mertunsaldi/me462_hockey/Duvar Tasarımları/Bekirhan_Duvar/Bekirhan_Duvar_Tasarimi/Duvar_Tasarimi_Bekirin_Fikri_Top_View.jpg

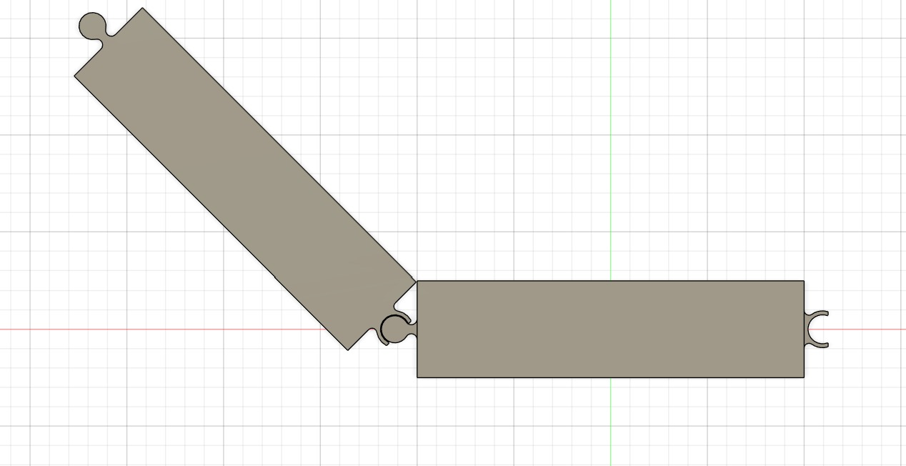
Duvar Tasarımları/Bekirhan_Duvar/Bekirhan_Duvar_Tasarimi/Duvar_Tasarimi_Bekirin_Fikri_Top_View.jpg
