mertunsaldi/me462_hockey/Duvar Tasarımları/Bekirhan_Duvar/Bekirhan_Duvar_Tasarimi/Duvar_Tasarimi_Mertin_Fikri_Iso_View.jpg

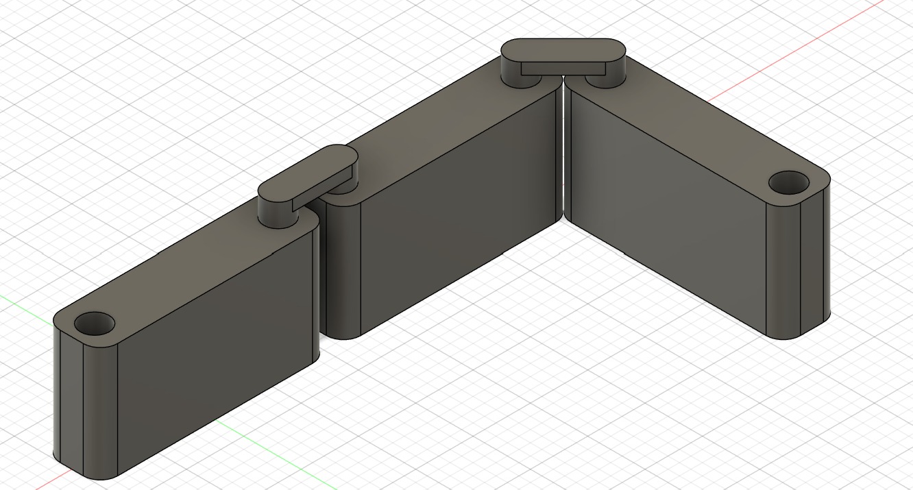
Duvar Tasarımları/Bekirhan_Duvar/Bekirhan_Duvar_Tasarimi/Duvar_Tasarimi_Mertin_Fikri_Iso_View.jpg
