mertunsaldi/me462_hockey/Duvar Tasarımları/Fatih/feet1_iso.png

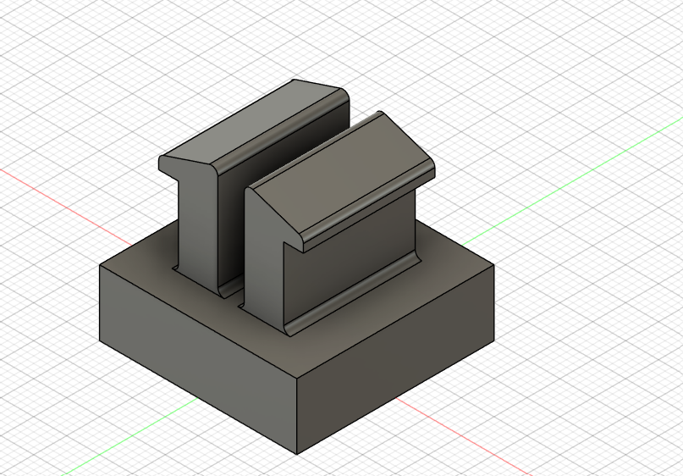
Duvar Tasarımları/Fatih/feet1_iso.png
