mertunsaldi/me462_hockey/Duvar Tasarımları/Fatih/assembly_0deg.png

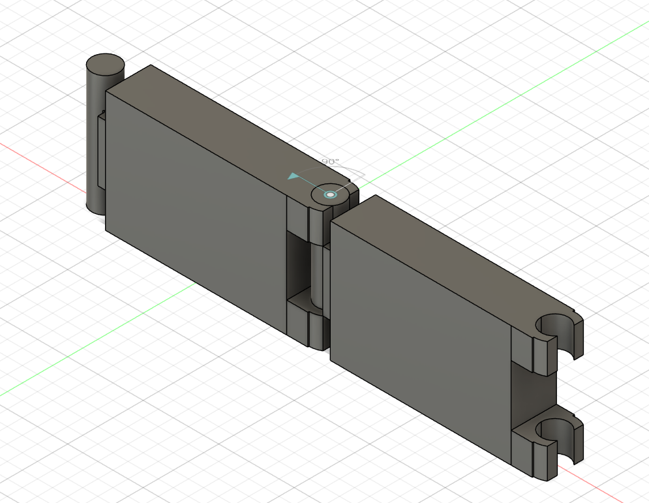
Duvar Tasarımları/Fatih/assembly_0deg.png
