mertunsaldi/me462_hockey/Duvar Tasarımları/Fatih/assembly_90deg_iso.png

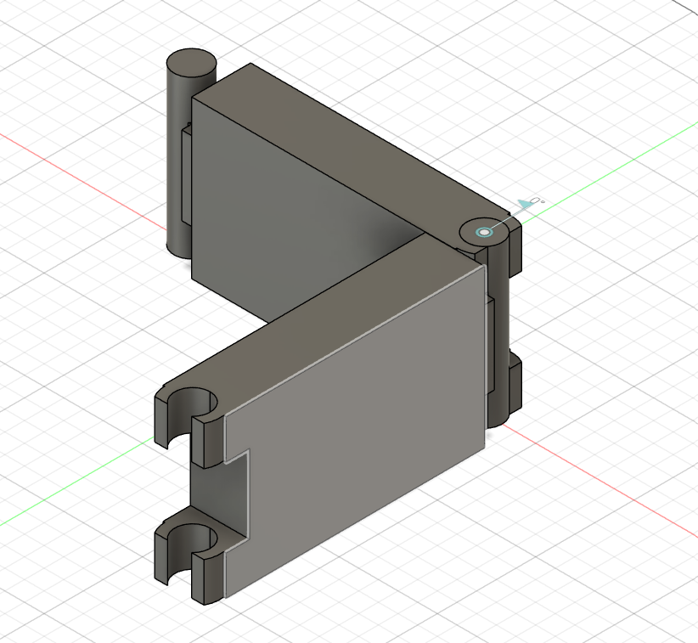
Duvar Tasarımları/Fatih/assembly_90deg_iso.png
