mertunsaldi/me462_hockey/Duvar Tasarımları/Fatih/assembly_90deg_top.png

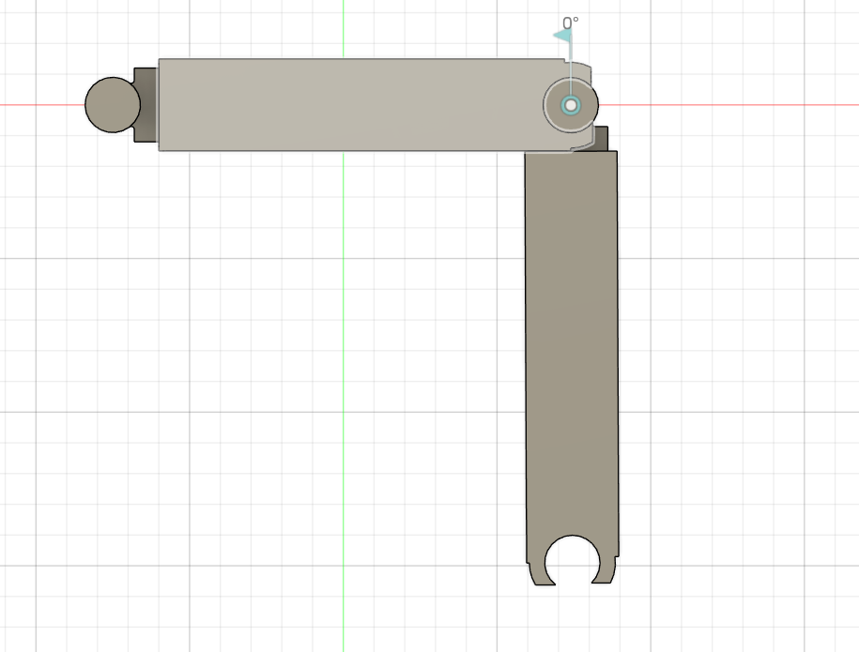
Duvar Tasarımları/Fatih/assembly_90deg_top.png
