mertunsaldi/me462_hockey/Duvar Tasarımları/Seckin/Assembly.png

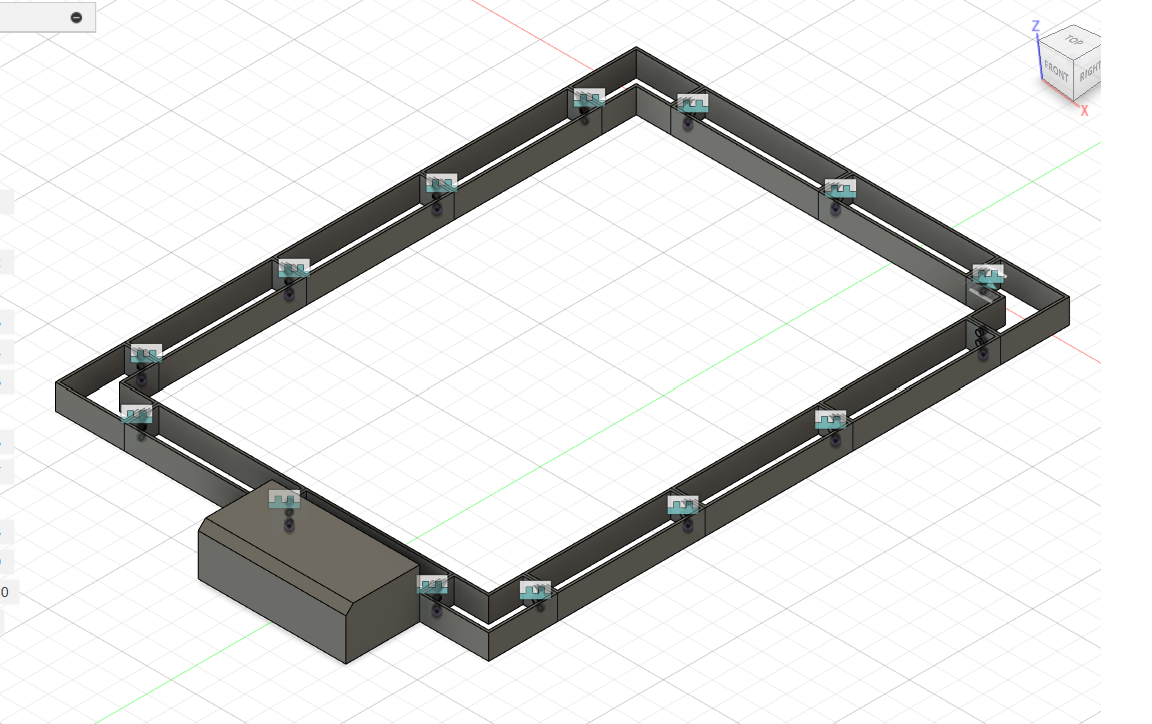
Duvar Tasarımları/Seckin/Assembly.png
