mertunsaldi/me462_hockey/ball_example/app.py

import cv2, math, threading, time
import numpy as np
from typing import Optional
from flask import Flask, render_template, Response, jsonify, request
import os

if __package__ in (None, ""):
    import os, sys
    sys.path.insert(0, os.path.abspath(os.path.join(os.path.dirname(__file__), "..")))
    __package__ = "ball_example"

from ball_example.game_api import GameAPI
from ball_example.scenario_loader import ScenarioLoadError
from ball_example.detectors import BallDetector, compute_color_mask, ArucoDetector
from ball_example.trackers import DETECTION_SCALE
from ball_example.models import ArucoWall, Arena, Obstacle, PhysicalTarget
from ball_example.gadgets import ArenaManager, PlotClock
from ball_example.high_level import calibrate_clocks, draw_arena

app = Flask(__name__, template_folder="templates", static_folder="static")

import logging

log = logging.getLogger("werkzeug")
log.setLevel(logging.ERROR)

# Core processing API
POLY_PATH = os.path.abspath(
    os.path.join(os.path.dirname(__file__), "..", "PlotClock", "calibration_poly.csv")
)
api = GameAPI(coeffs_path=POLY_PATH)
api.set_cam_source(4, width=1280, height=720, fourcc="MJPG")

if hasattr(app, "before_first_request"):
    @app.before_first_request
    def _ensure_camera_running():
        api.start()
else:
    @app.before_request
    def _ensure_camera_running():
        api.start()
        
# Manual tuning state
manual_mode = False
detected_clocks = []
detected_arena = None
_default_params = {
    "circ": BallDetector.CIRCULARITY_THRESHOLD,
    "area_ratio": BallDetector.AREA_RATIO_THRESHOLD,
    "solidity": BallDetector.SOLIDITY_THRESHOLD,
    "edge_density": BallDetector.EDGE_DENSITY_THRESHOLD,
    "blur": BallDetector.BLUR_KERNEL,
    "sigma": BallDetector.BLUR_SIGMA,
    "min_r": BallDetector.MIN_RADIUS,
    "max_r": BallDetector.MAX_RADIUS,
    "h_low": int(BallDetector.HSV_LOWER[0]),
    "s_low": int(BallDetector.HSV_LOWER[1]),
    "v_low": int(BallDetector.HSV_LOWER[2]),
    "h_up": int(BallDetector.HSV_UPPER[0]),
    "s_up": int(BallDetector.HSV_UPPER[1]),
    "v_up": int(BallDetector.HSV_UPPER[2]),
}
_manual_params = _default_params.copy()

def _apply_params(params):
    BallDetector.CIRCULARITY_THRESHOLD = float(params["circ"])
    BallDetector.AREA_RATIO_THRESHOLD  = float(params["area_ratio"])
    BallDetector.SOLIDITY_THRESHOLD    = float(params["solidity"])
    BallDetector.BLUR_KERNEL = int(params["blur"])
    BallDetector.BLUR_SIGMA  = float(params["sigma"])
    BallDetector.EDGE_DENSITY_THRESHOLD= float(params["edge_density"])
    BallDetector.MIN_RADIUS = int(params["min_r"])
    BallDetector.MAX_RADIUS = int(params["max_r"])
    BallDetector.HSV_LOWER = np.array([params["h_low"], params["s_low"], params["v_low"]], dtype=np.uint8)
    BallDetector.HSV_UPPER = np.array([params["h_up"], params["s_up"], params["v_up"]], dtype=np.uint8)

def _reset_defaults():
    global _manual_params
    _manual_params = _default_params.copy()
    _apply_params(_default_params)


# ------------------------------------------------------------------


@app.route("/start_scenario", methods=["POST"])
def start_scenario():
    """Activate the currently loaded scenario."""
    try:
        api.start_scenario()
        return jsonify({"status": "ok"})
    except Exception as e:
        return jsonify({"status": "error", "message": str(e)}), 400


@app.route("/stop_scenario", methods=["POST"])
def stop_scenario():
    """Deactivate the running scenario if any."""
    try:
        api.stop_scenario()
        return jsonify({"status": "ok"})
    except Exception as e:
        return jsonify({"status": "error", "message": str(e)}), 400


@app.route("/load_commands", methods=["POST"])
def load_commands():
    data = request.get_json(silent=True) or {}
    commands = data.get("commands")
    if not isinstance(commands, list):
        return jsonify({"status": "error", "message": "commands must be a list"}), 400
    try:
        api.load_commands(commands)
        return jsonify({"status": "ok"})
    except Exception as e:
        return jsonify({"status": "error", "message": str(e)}), 400


@app.route("/load_scenario", methods=["POST"])
def load_scenario_route():
    """Load a custom scenario from a Python file path or uploaded file."""
    if "file" in request.files:
        up = request.files["file"]
        path = "/tmp/" + up.filename
        up.save(path)
    else:
        data = request.get_json(silent=True) or {}
        path = data.get("path")
    if not path:
        return jsonify({"status": "error", "message": "no path provided"}), 400
    try:
        api.load_scenario(path)
        return jsonify({"status": "ok"})
    except ScenarioLoadError as e:
        return jsonify({"status": "error", "message": str(e)}), 400
    except RuntimeError as e:
        # allow missing plotclock during testing
        return jsonify({"status": "error", "message": str(e)})
    except Exception as e:
        return jsonify({"status": "error", "message": str(e)}), 500




def generate_frames():
    while True:
        annotated = api.get_annotated_frame()
        if annotated is None:
            time.sleep(0.01)
            continue

        with api.lock:
            dets = api.balls + api.arucos

        if detected_arena:
            draw_arena(annotated, detected_arena)
        for c in detected_clocks:
            c.draw_working_area(annotated)

        ok, buf = cv2.imencode(".jpg", annotated)
        if not ok:
            continue

        yield (
            b"--frame\r\n" b"Content-Type: image/jpeg\r\n\r\n" + buf.tobytes() + b"\r\n"
        )



@app.route("/")
def index():
    return render_template("index.html")


@app.route("/video_feed")
def video_feed():
    return Response(
        generate_frames(), mimetype="multipart/x-mixed-replace; boundary=frame"
    )


@app.route("/debug_data")
def debug_data():
    """Return extended diagnostic information."""
    return jsonify(api.debug_info())


@app.route("/connect_pico", methods=["POST"])
def connect_pico():
    global detected_clocks, detected_arena
    try:
        api.connect_pico()

        print("Waiting for detections...")
        detected_clocks = []
        detected_arena = None
        start = time.time()
        while time.time() - start < 5:
            time.sleep(0.1)
            with api.lock:
                detections = list(api.arucos)
                detected_clocks = list(api.plotclocks.values())
            if detected_arena is None:
                walls = [d for d in detections if isinstance(d, ArucoWall)]
                if walls:
                    detected_arena = Arena(walls)

        if detected_arena:
            for c in detected_clocks:
                if isinstance(c, ArenaManager):
                    c.set_arena(detected_arena)

        if detected_clocks:
            stable_start = time.time()
            last_count = len(detected_clocks)
            while time.time() - stable_start < 1.0:
                time.sleep(0.1)
                with api.lock:
                    detected_clocks = list(api.plotclocks.values())
                if len(detected_clocks) == last_count:
                    break
                last_count = len(detected_clocks)
                stable_start = time.time()

        # if both a manager (P0) and a hitter (P1) are detected, prepare the
        # built-in default scenario so it can be started via the UI
        manager = next(
            (c for c in detected_clocks if isinstance(c, ArenaManager) and c.device_id == 0),
            None,
        )
        hitter = next(
            (c for c in detected_clocks if isinstance(c, PlotClock) and c.device_id == 1),
            None,
        )
        if manager and hitter:
            api.default_scenario = "MoveBallHitRandom"
            api.load_default_scenario()
        else:
            api.default_scenario = None

        return jsonify({"status": "ok"})
    except Exception as e:
        return jsonify({"status": "error", "message": str(e)}), 500


@app.route("/calibrate_all", methods=["POST"])
def calibrate_all():
    """Calibrate all detected PlotClocks."""
    global detected_clocks
    with api.lock:
        clocks = list(api.plotclocks.values())
    if not clocks:
        return jsonify({"status": "error", "message": "no plotclocks"}), 400

    detected_clocks = clocks

    def _get_dets():
        with api.lock:
            return api.balls + api.arucos

    calibrate_clocks(clocks, _get_dets)
    return jsonify({"status": "ok"})


@app.route("/toggle_mode", methods=["POST"])
def toggle_mode():
    """Start or stop a scenario for a specific PlotClock."""
    data = request.get_json(silent=True) or {}
    device_id = int(data.get("device_id", -1))
    mode = data.get("mode")
    clock = api.plotclocks.get(device_id)
    if clock is None or mode not in {"attack", "defend", "hit_standing"}:
        return jsonify({"status": "error", "message": "invalid"}), 400

    x_mm = y_mm = None
    if mode in {"attack", "hit_standing"}:
        try:
            x_mm = float(data.get("x"))
            y_mm = float(data.get("y"))
        except (TypeError, ValueError):
            return jsonify({"status": "error", "message": "invalid"}), 400

    if api.clock_modes.get(device_id) == mode:
        api.stop_clock_mode(device_id)
        return jsonify({"status": "stopped"})

    # replace any running scenario on this clock
    if device_id in api.clock_scenarios:
        api.stop_clock_mode(device_id)

    api.start_clock_mode(clock, mode, target_mm=(x_mm, y_mm))
    api.set_preview_target(device_id, (x_mm, y_mm)) if x_mm is not None else None
    return jsonify({"status": "started"})


@app.route("/move_object", methods=["POST"])
def move_object_route():
    data = request.get_json(silent=True) or {}
    device_id = int(data.get("device_id", -1))
    obj_spec = data.get("object")
    try:
        x_mm = float(data.get("x"))
        y_mm = float(data.get("y"))
    except (TypeError, ValueError):
        return jsonify({"status": "error", "message": "invalid"}), 400
    with api.lock:
        manager = api.plotclocks.get(device_id)
        if not isinstance(manager, ArenaManager):
            return jsonify({"status": "error", "message": "invalid"}), 400
        if not obj_spec:
            return jsonify({"status": "error", "message": "invalid"}), 400

        if obj_spec.startswith("ball:"):
            bid = obj_spec.split(":", 1)[1]
            obj = next((b for b in api.balls if b.id == bid), None)
        elif obj_spec.startswith("obs:"):
            oid = int(obj_spec.split(":", 1)[1])
            obstacles = [m for m in api.arucos if isinstance(m, Obstacle)]
            obj = obstacles[oid] if 0 <= oid < len(obstacles) else None
        elif obj_spec.startswith("tgt:"):
            tid = int(obj_spec.split(":", 1)[1])
            targets = [m for m in api.arucos if isinstance(m, PhysicalTarget)]
            obj = targets[tid] if 0 <= tid < len(targets) else None
        else:
            obj = None

    if obj is None:
        return jsonify({"status": "error", "message": "not found"}), 400

    if device_id in api.clock_scenarios:
        api.stop_clock_mode(device_id)

    api.start_move_object(manager, obj, (x_mm, y_mm))
    api.set_preview_target(device_id, (x_mm, y_mm))
    return jsonify({"status": "started"})


@app.route("/move_manager", methods=["POST"])
def move_manager_route():
    data = request.get_json(silent=True) or {}
    device_id = int(data.get("device_id", -1))
    try:
        x_px = int(data.get("x"))
        y_px = int(data.get("y"))
    except (TypeError, ValueError):
        return jsonify({"status": "error", "message": "invalid"}), 400

    with api.lock:
        manager = api.plotclocks.get(device_id)
        scenario_running = api._current_scenario is not None and api.scenario_enabled
    print(
        f"move_manager req dev={device_id} px=({x_px},{y_px}) scenario_loaded={scenario_running}"
    )

    if not isinstance(manager, ArenaManager):
        return jsonify({"status": "error", "message": "not connected"}), 400

    if scenario_running:
        print("scenario is running, rejecting move")
        return jsonify({"status": "error", "message": "scenario running"}), 400

    if manager.calibration is None:
        return jsonify({"status": "error", "message": "uncalibrated"}), 400

    try:
        x_mm, y_mm = manager.pixel_to_mm((x_px, y_px))
    except Exception as e:
        print("pixel_to_mm failed", e)
        return jsonify({"status": "error", "message": str(e)}), 400
    print(f"converted to mm=({x_mm:.2f},{y_mm:.2f})")

    print(f"sending manager move to ({x_mm:.2f}, {y_mm:.2f})")
    # use feedback-enhanced move for arena manager
    manager.setXY_updated_manager(x_mm, y_mm)
    api.set_preview_target(device_id, (x_mm, y_mm))
    print("preview target set")
    return jsonify({"status": "ok", "x_mm": x_mm, "y_mm": y_mm})


@app.route("/select_object", methods=["POST"])
def select_object_route():
    data = request.get_json(silent=True) or {}
    obj = data.get("object")
    if not obj:
        api.set_selected_object(None)
    else:
        try:
            obj_type, obj_id = obj.split(":", 1)
            api.set_selected_object((obj_type, obj_id))
        except Exception:
            return jsonify({"status": "error", "message": "invalid"}), 400
    return jsonify({"status": "ok"})


@app.route("/preview_target", methods=["POST"])
def preview_target_route():
    data = request.get_json(silent=True) or {}
    device_id = int(data.get("device_id", -1))
    with api.lock:
        clock = api.plotclocks.get(device_id)
        if clock is None:
            return jsonify({"status": "error", "message": "invalid"}), 400

    try:
        x_mm = float(data.get("x"))
        y_mm = float(data.get("y"))
    except (TypeError, ValueError):
        api.clear_preview_target(device_id)
        return jsonify({"status": "ok"})

    api.set_preview_target(device_id, (x_mm, y_mm))
    return jsonify({"status": "ok"})


@app.route("/send_cmd", methods=["POST"])
def send_cmd():
    try:
        api.connect_pico()
    except Exception:
        return jsonify({"status": "error", "message": "not connected"}), 400
    data = request.get_json(silent=True) or {}
    cmd = data.get("cmd", "").strip()
    if not cmd:
        return jsonify({"status": "error", "message": "empty cmd"}), 400
    try:
        api.send_cmd(cmd)
        return jsonify({"status": "ok"})
    except Exception as e:
        return jsonify({"status": "error", "message": str(e)}), 500


@app.route("/pico_lines")
def pico_lines():
    lines = api.read_pico_lines()
    return jsonify({"lines": lines})


@app.route("/send_message", methods=["POST"])
def send_message():
    """Dispatch a control message to the running scenario."""
    data = request.get_json(silent=True) or {}
    try:
        api.process_message(data)
        return jsonify({"status": "ok"})
    except Exception as e:
        return jsonify({"status": "error", "message": str(e)}), 400


@app.route("/tune")
def tune_page():
    return render_template("tune.html")


@app.route("/debug")
def debug_page():
    """Display debugging information."""
    return render_template("debug.html")


@app.route("/manual_params", methods=["GET", "POST"])
def manual_params_route():
    global manual_mode, _manual_params
    if request.method == "GET":
        return jsonify({"manual": manual_mode, **_manual_params})
    data = request.get_json(silent=True) or {}
    param = data.get("param")
    value = data.get("value")
    if param not in _manual_params:
        return jsonify({"status": "error", "message": "bad param"}), 400
    _manual_params[param] = value
    if manual_mode:
        _apply_params(_manual_params)
        frame = api.raw_pipe.get_raw_frame()
        mask = compute_color_mask(frame, scale=DETECTION_SCALE) if frame is not None else None
        markers = ArucoDetector.detect(frame) if frame is not None else []
        if frame is not None:
            api.tracker_mgr.force_redetect(frame, mask=mask, markers=markers)
    return jsonify({"status": "ok"})


@app.route("/manual_mode", methods=["POST"])
def manual_mode_route():
    global manual_mode
    data = request.get_json(silent=True) or {}
    enable = bool(data.get("enable"))
    manual_mode = enable
    if manual_mode:
        _apply_params(_manual_params)
    else:
        _reset_defaults()
    frame = api.raw_pipe.get_raw_frame()
    mask = compute_color_mask(frame, scale=DETECTION_SCALE) if frame is not None else None
    markers = ArucoDetector.detect(frame) if frame is not None else []
    if frame is not None:
        api.tracker_mgr.force_redetect(frame, mask=mask, markers=markers)
    return jsonify({"status": "ok", "manual": manual_mode})


if __name__ == "__main__":
    try:
        api.start()
        app.run(host="0.0.0.0", port=8000, threaded=True, debug=False, use_reloader=False)
    finally:
        if api.annotated_pipe:
            api.annotated_pipe.stop()
        api.raw_pipe.stop()
        api.camera.stop()
